monash-wsrn/ebug2014-pcb/Documents/Parts/SMD 16-Pos Socket/SSW-SVS.PDF

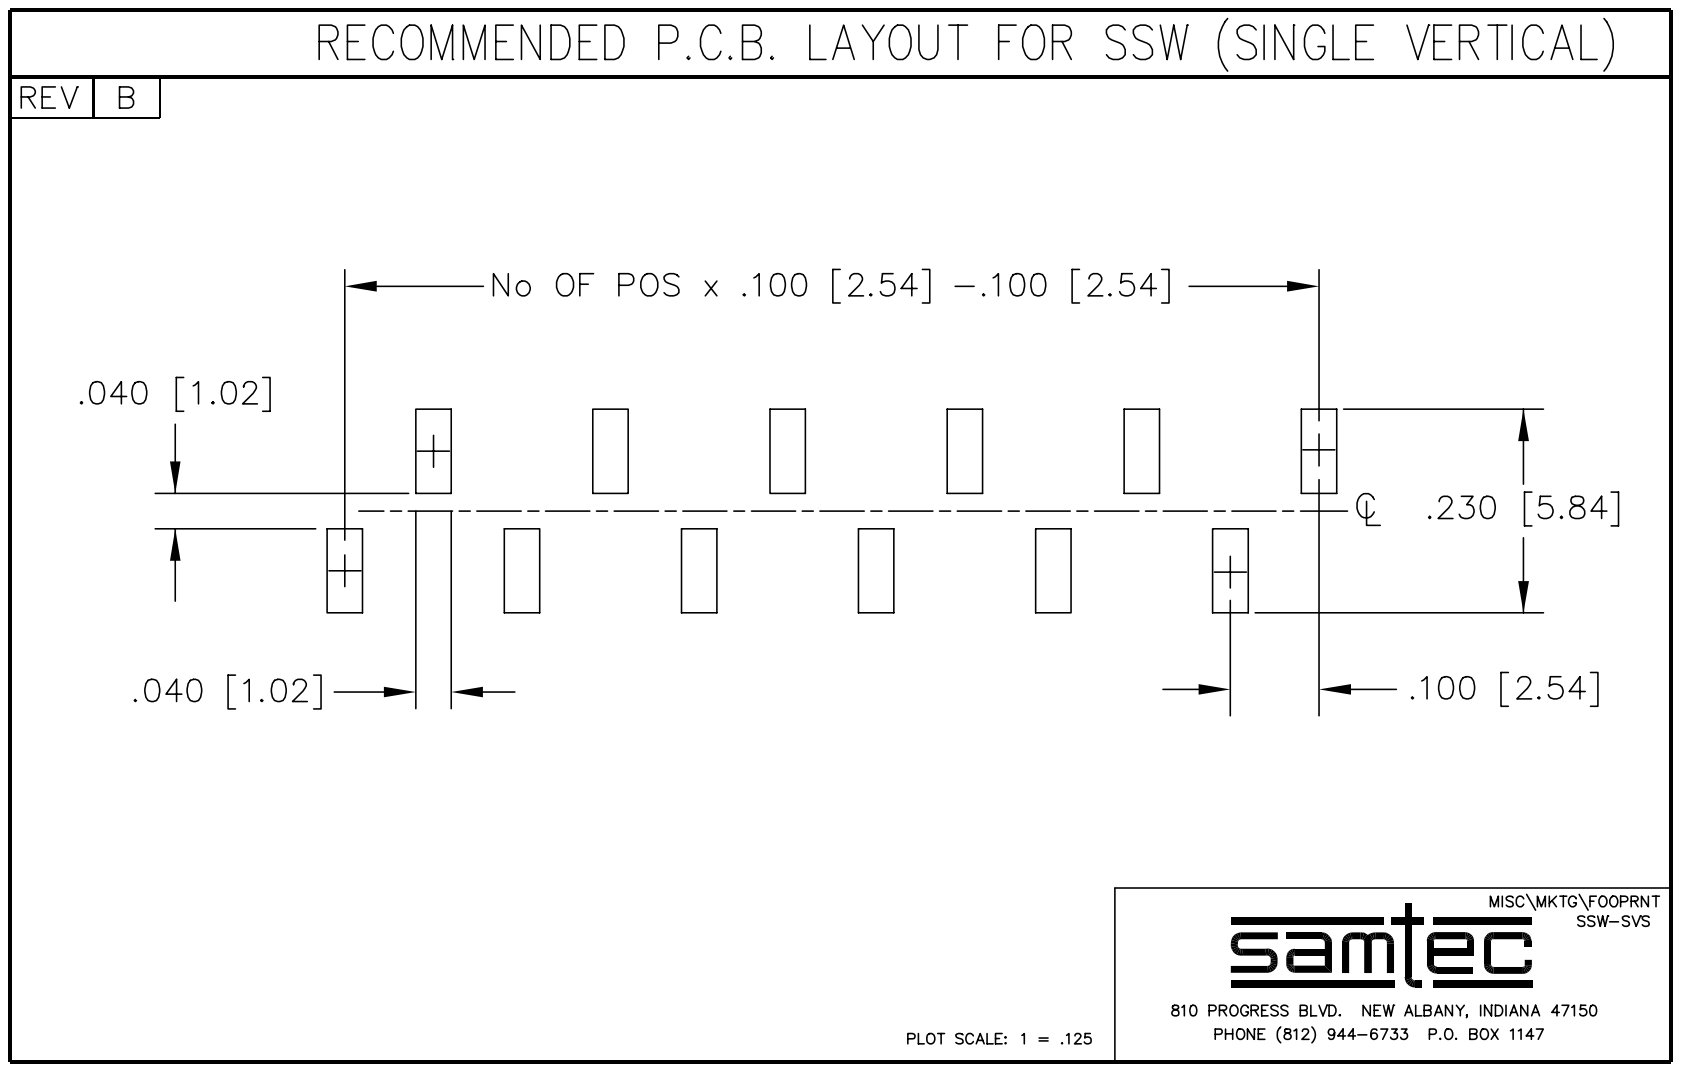
[picture p11: page 1]
