monash-wsrn/ebug2014-pcb/Documents/Parts/FFC Connector/TE/ENG_CD_1734592_C_C_1734592.pdf

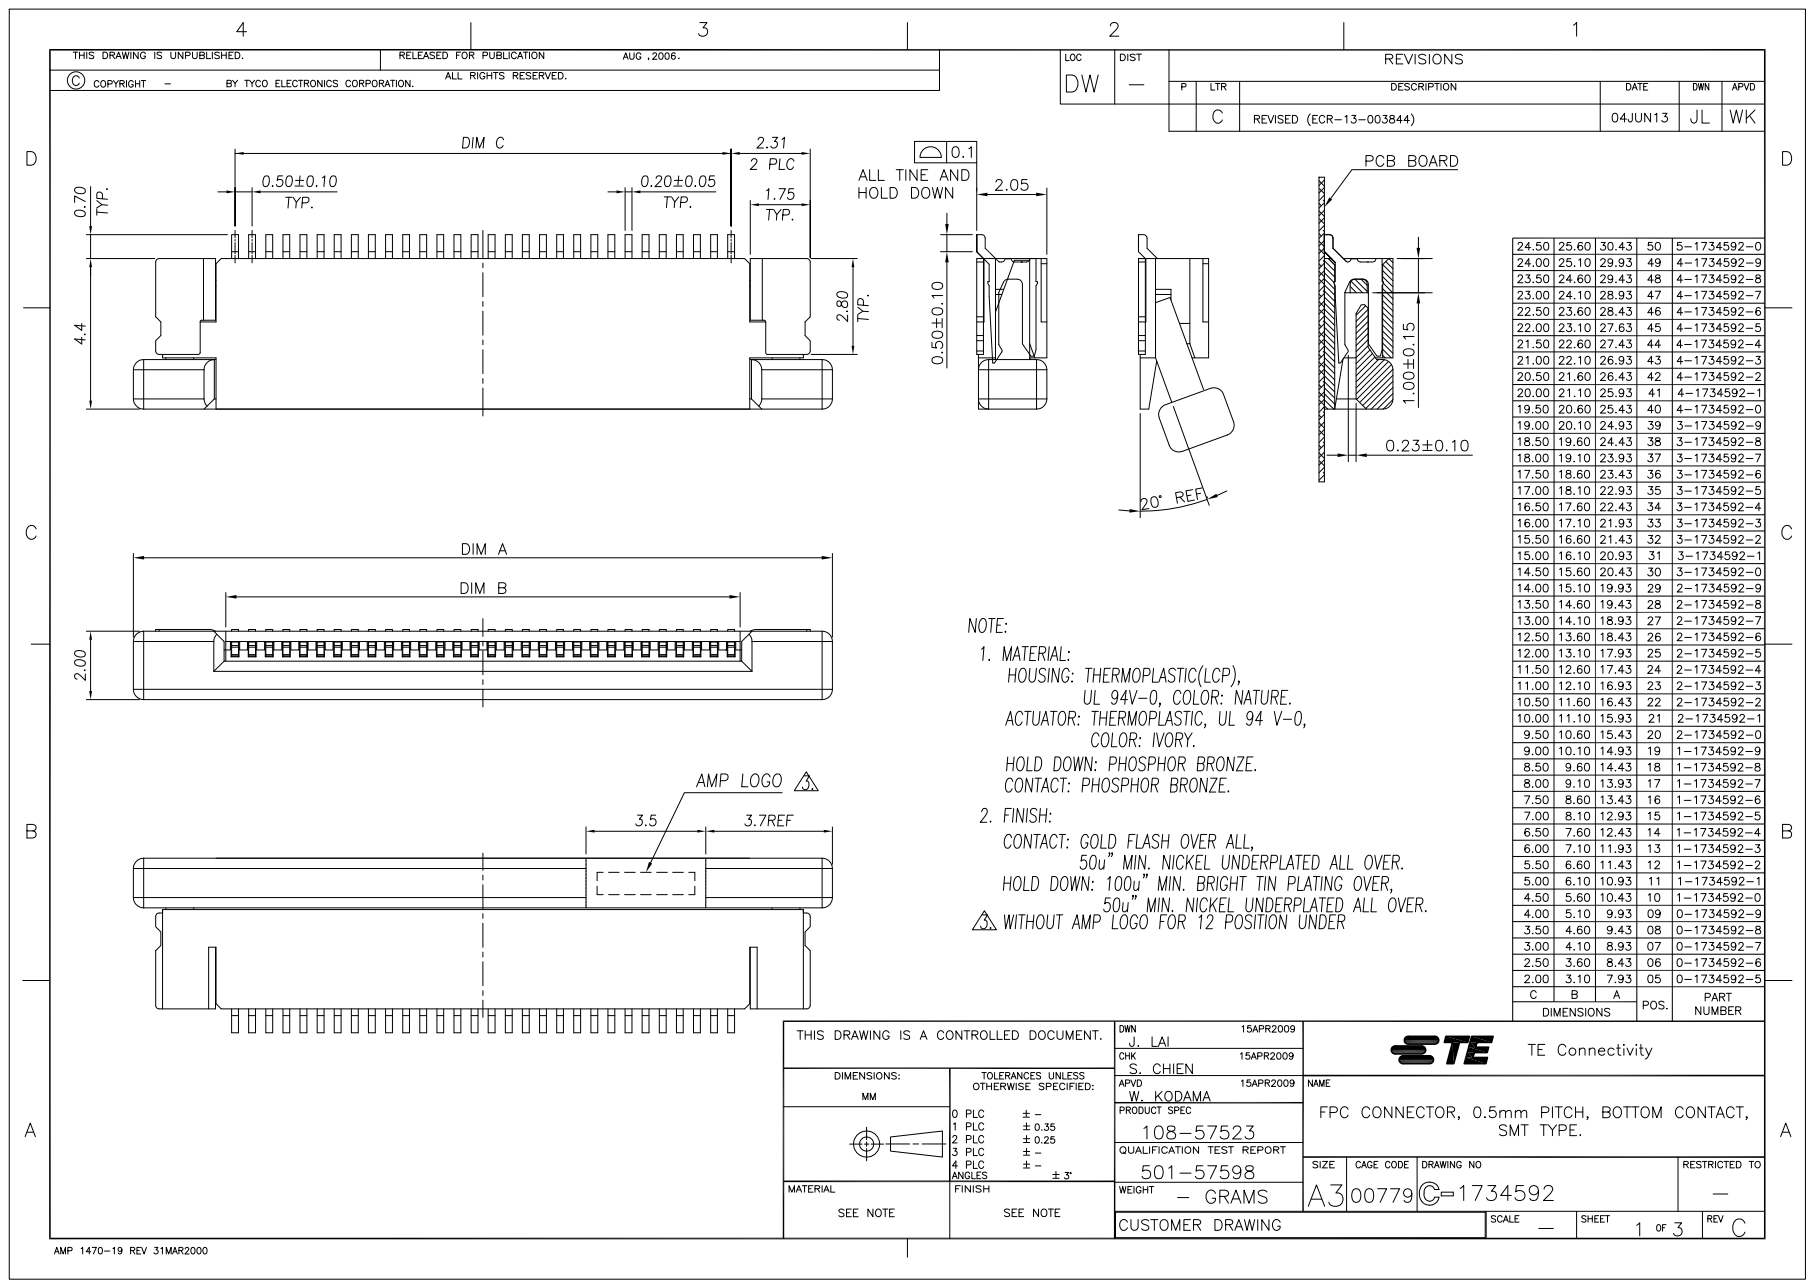
[picture p12: page 1]

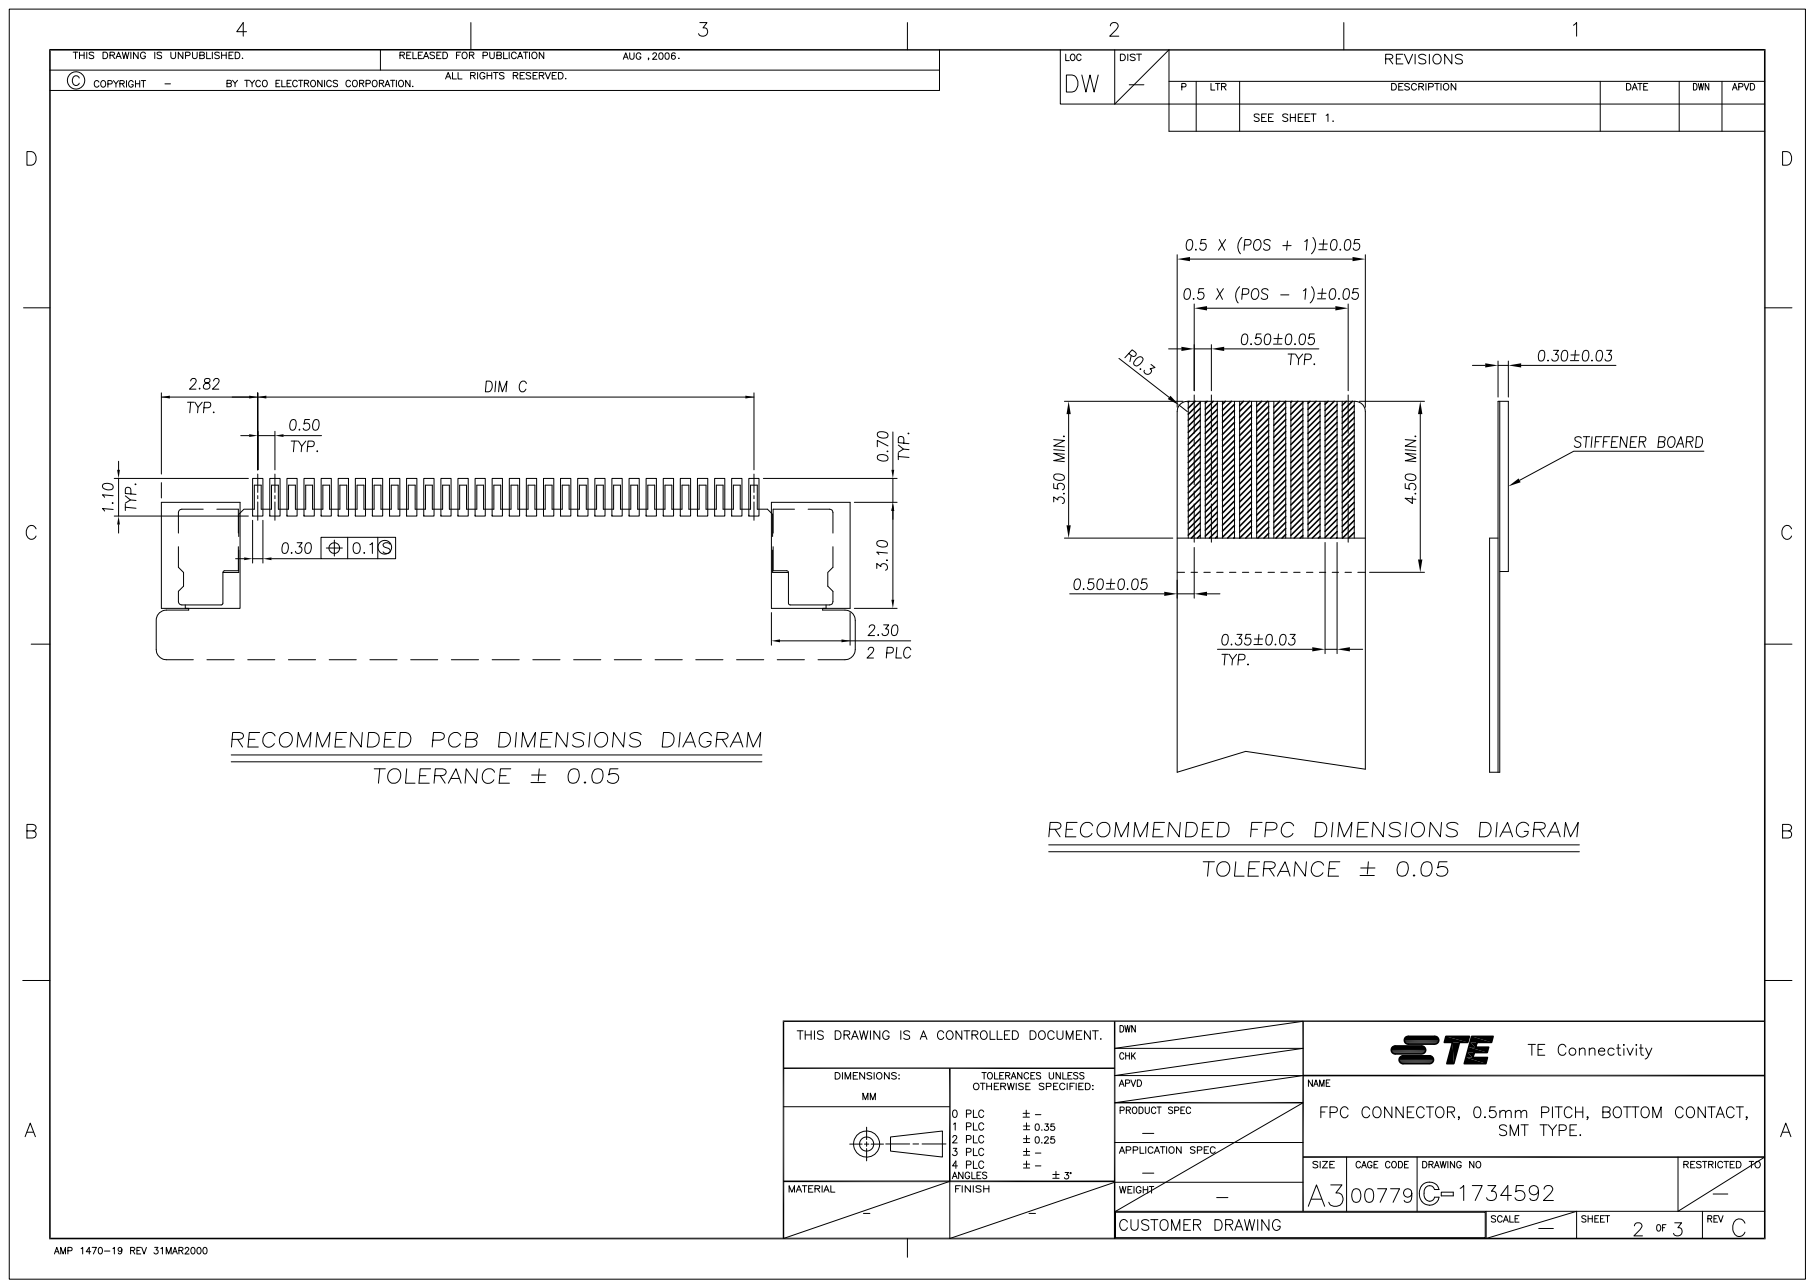
[picture p13: page 2]

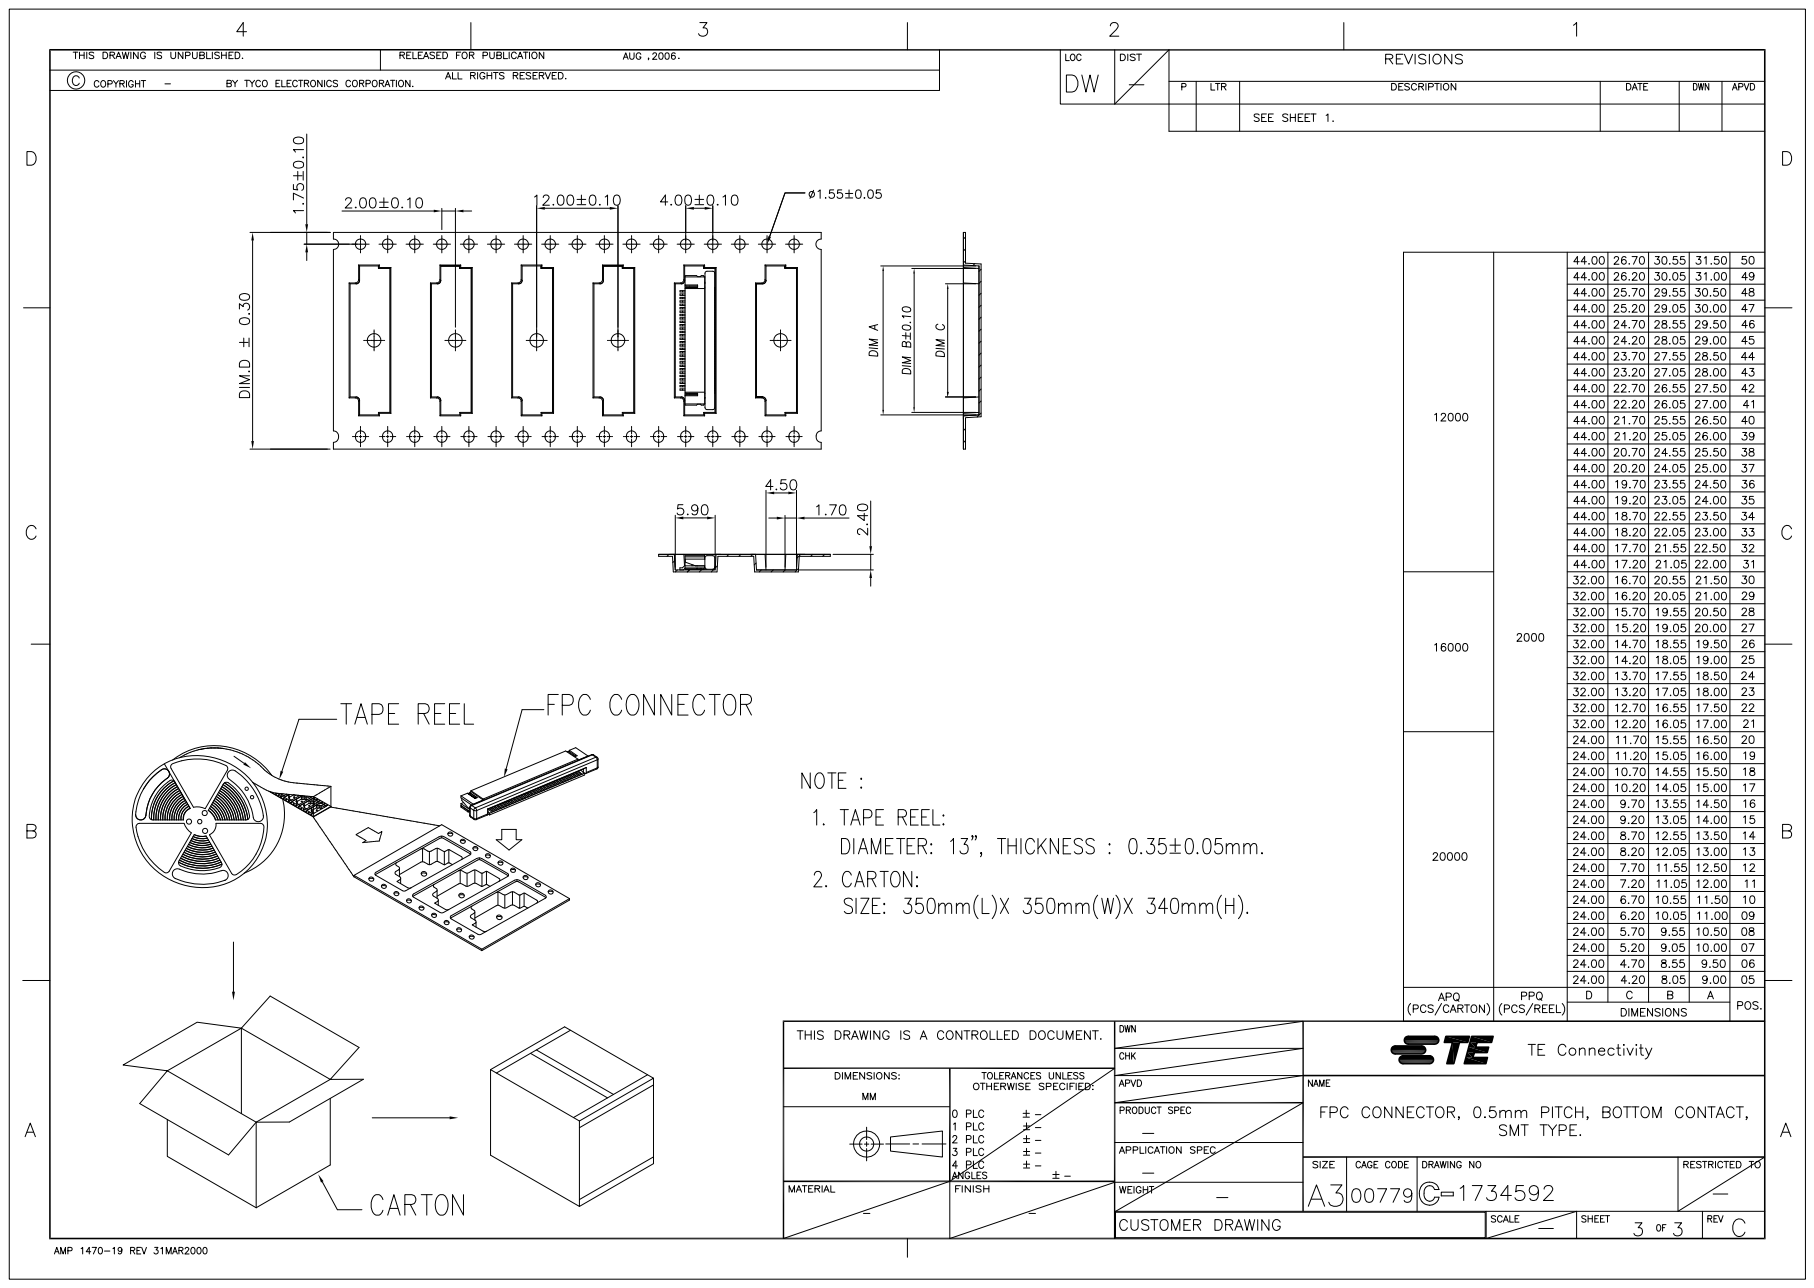
[picture p14: page 3]
