monash-wsrn/ebug2014-pcb/Documents/Parts/Battery Holder/1042/1042P.PDF

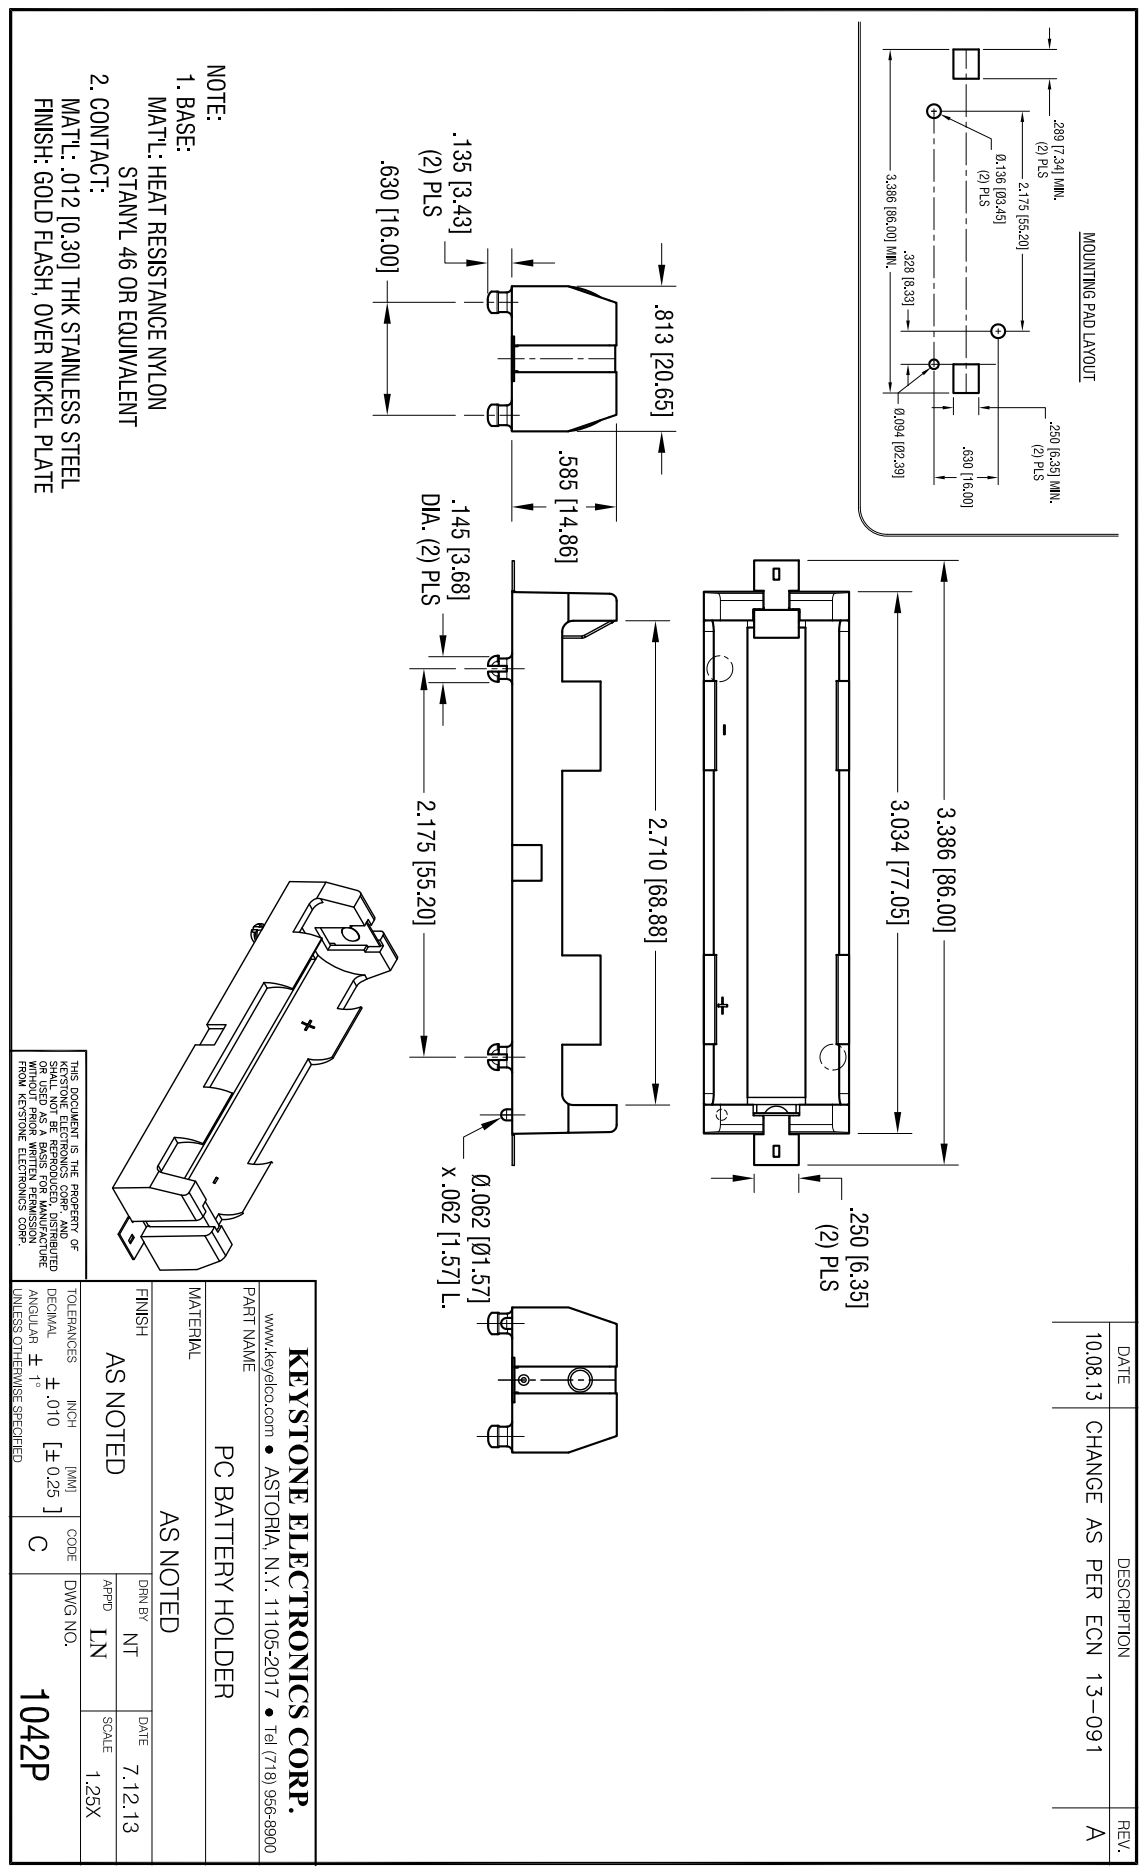
[picture p15: page 1]
